LukeBuonanno/Spot/micross7pt7b.h

const uint8_t micross7pt7bBitmaps[] PROGMEM = {
  0x00, 0xFF, 0x40, 0xB6, 0xD0, 0x12, 0x12, 0x22, 0x7F, 0x24, 0x24, 0xFE,
  0x48, 0x48, 0x48, 0x11, 0xE9, 0x64, 0x91, 0xE2, 0x49, 0x26, 0x97, 0x88,
  0x70, 0x22, 0x28, 0x92, 0x28, 0x74, 0x02, 0xE1, 0x44, 0x91, 0x44, 0x40,
  0xE0, 0x30, 0x91, 0x22, 0xC2, 0x0A, 0x62, 0xC2, 0x84, 0xF4, 0xF0, 0x29,
  0x49, 0x24, 0x91, 0x22, 0x89, 0x12, 0x49, 0x25, 0x28, 0x27, 0xC8, 0xA0,
  0x10, 0x20, 0x47, 0xF1, 0x02, 0x04, 0x00, 0x58, 0xF0, 0x80, 0x11, 0x22,
  0x24, 0x44, 0x88, 0x7A, 0x18, 0x61, 0x86, 0x18, 0x61, 0x85, 0xE0, 0x3C,
  0x92, 0x49, 0x24, 0x7A, 0x18, 0x41, 0x08, 0x42, 0x10, 0x83, 0xF0, 0x7A,
  0x18, 0x41, 0x38, 0x10, 0x61, 0x85, 0xE0, 0x08, 0x62, 0x8A, 0x4A, 0x2F,
  0xC2, 0x08, 0x20, 0xFE, 0x08, 0x2E, 0xC4, 0x10, 0x61, 0x85, 0xE0, 0x01,
  0xE8, 0x61, 0x82, 0xEC, 0x61, 0x86, 0x17, 0x80, 0xFC, 0x10, 0x42, 0x08,
  0x41, 0x04, 0x21, 0x80, 0x7A, 0x18, 0x61, 0x7A, 0x18, 0x61, 0x85, 0xE0,
  0x7A, 0x18, 0x61, 0x8D, 0xD0, 0x61, 0x85, 0xE0, 0x00, 0x82, 0x40, 0x05,
  0x80, 0x04, 0x66, 0x20, 0x60, 0x60, 0x40, 0xFC, 0x00, 0x3F, 0x81, 0x81,
  0x81, 0x19, 0x88, 0x00, 0x7A, 0x18, 0x41, 0x08, 0x41, 0x04, 0x00, 0x40,
  0x0F, 0x83, 0x06, 0x40, 0x24, 0x79, 0x88, 0x99, 0x09, 0x91, 0x19, 0x11,
  0x93, 0x24, 0xDC, 0x40, 0x03, 0x04, 0x0F, 0x80, 0x08, 0x04, 0x05, 0x02,
  0x82, 0x21, 0x11, 0xFC, 0x82, 0x80, 0xC0, 0x40, 0xFD, 0x06, 0x0C, 0x1F,
  0xD0, 0x60, 0xC1, 0x83, 0xF8, 0x3C, 0x42, 0x81, 0x80, 0x80, 0x80, 0x80,
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
  {   250,   7,  10,   8,    1,   -9 },   // 0x46 'F'
  {   259,   9,  10,  11,    1,   -9 },   // 0x47 'G'
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

const GFXfont micross7pt7b PROGMEM = {
  (uint8_t  *)micross7pt7bBitmaps,
  (GFXglyph *)micross7pt7bGlyphs,
  0x20, 0x7E, 16 };

// Approx. 1346 bytes
