LukeBuonanno/Spot/stop.h

#define STOP_HEIGHT 240
#define STOP_WIDTH 240

// array size is 115200
static const uint16_t stop[] PROGMEM = {
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
};
