LukeBuonanno/Spot/win98_clouds.h

#define RSZ_11WINDOWS_98_CLOUDS_1__HEIGHT 240
#define RSZ_11WINDOWS_98_CLOUDS_1__WIDTH 240

// array size is 115200
static const uint16_t rsz_11windows_98_clouds_1_[] PROGMEM  = {
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
};
